fifteenhex/sordplay/kicad/MX-MAIN-C/MX-MAIN-C.kicad_sch

## KiCad design kicad/MX-MAIN-C/MX-MAIN-C.kicad_sch (2026-04-12, an earlier design)

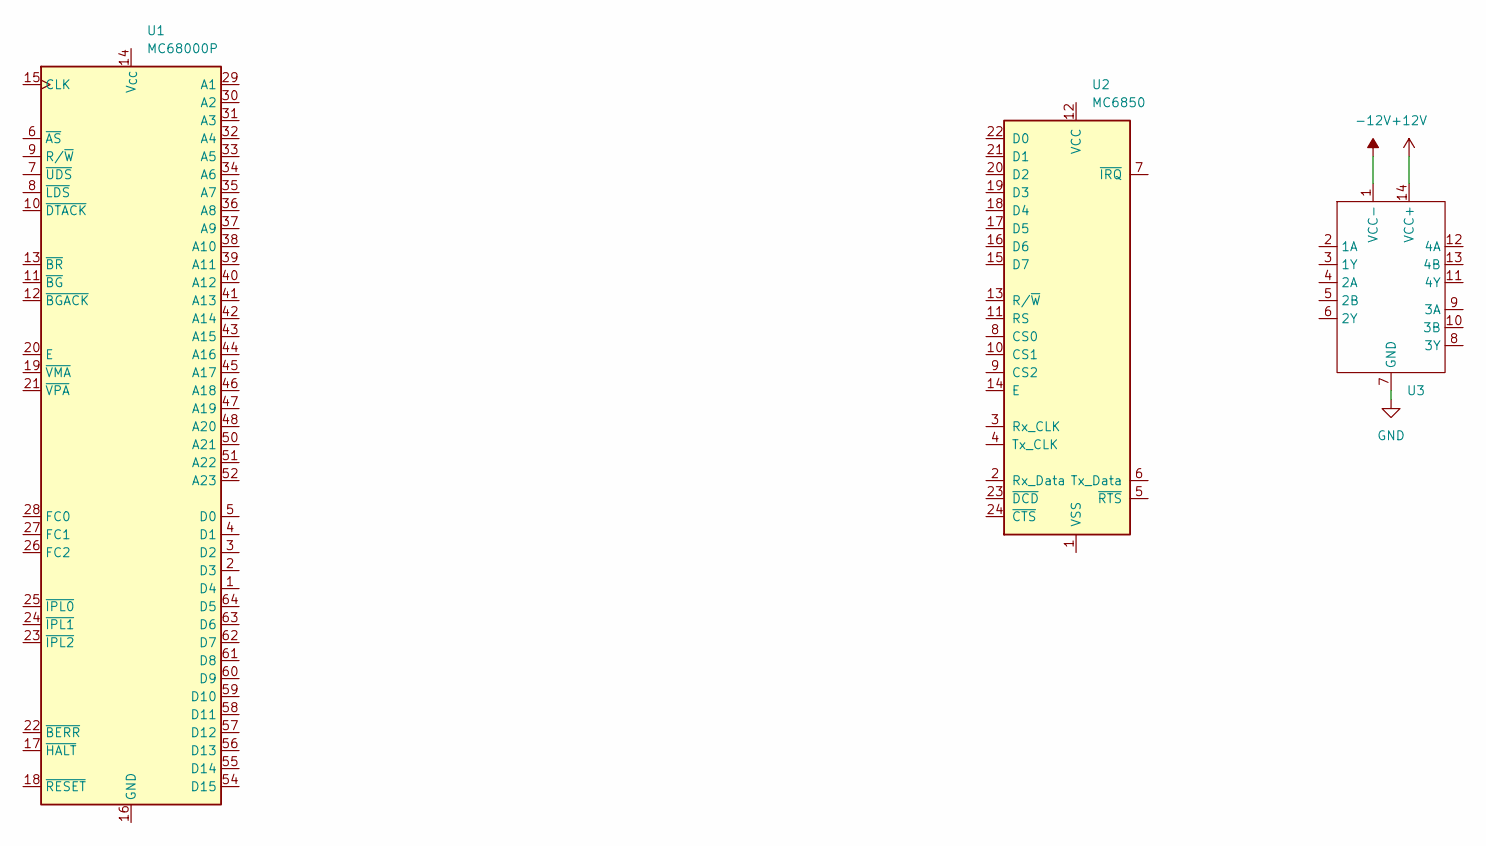
[picture p3: schematic MX-MAIN-C.kicad_sch]

Parts:
U1: MC68000P; DIP-64_W22.86mm
U2: MC6850; DIP-24_W15.24mm
U3: (no value)

Connections:
+12V: U3.14 (VCC+)
-12V: U3.1 (VCC-)
GND: U3.7 (GND)
unnamed: U1.14 (V_{CC}), U1.49 (V_{CC})
unnamed: U1.16 (GND), U1.53 (GND)
